Aries1A/kenagerobo/src/pyscript/Q_learning/img_forum/camera_capture_0.jpg

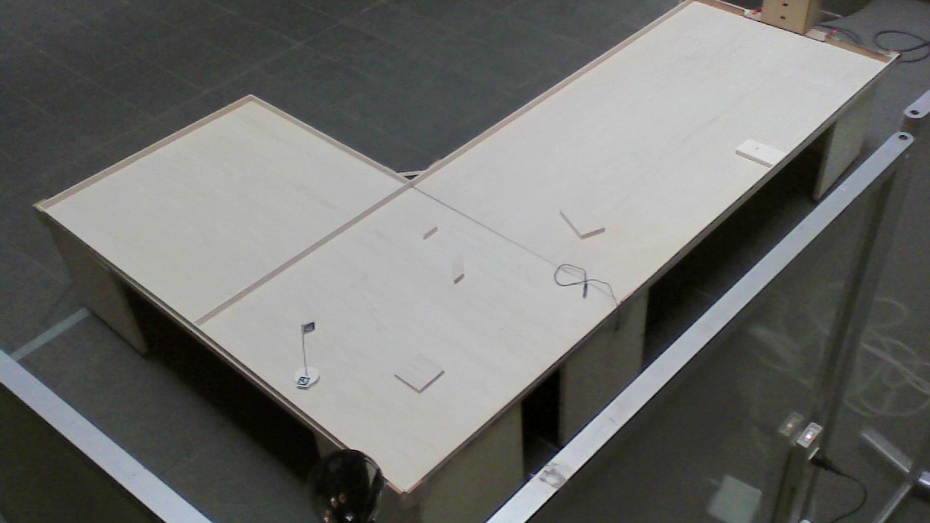
src/pyscript/Q_learning/img_forum/camera_capture_0.jpg
