Aries1A/kenagerobo/src/pyscript/Q_learning/imgs/img_forum/camera_capture_1.jpg

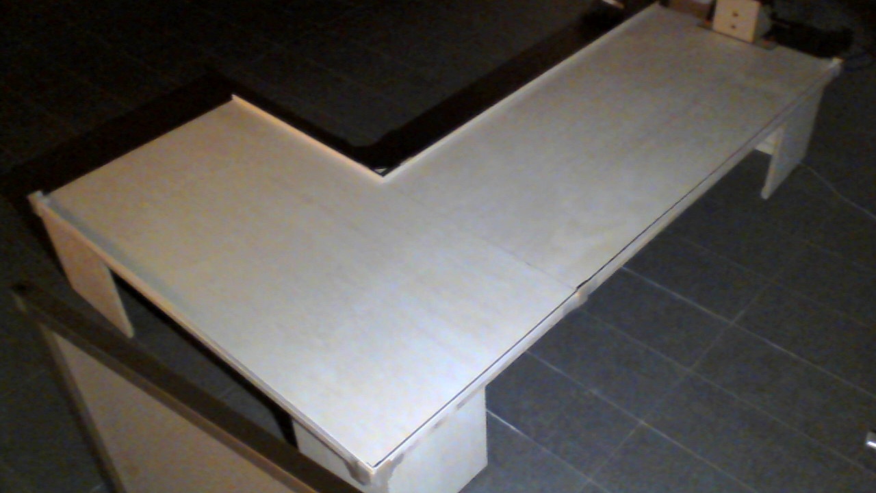
src/pyscript/Q_learning/imgs/img_forum/camera_capture_1.jpg
