Aries1A/kenagerobo/src/pyscript/Q_learning/imgs/img_forum_square/camera_capture_0.jpg

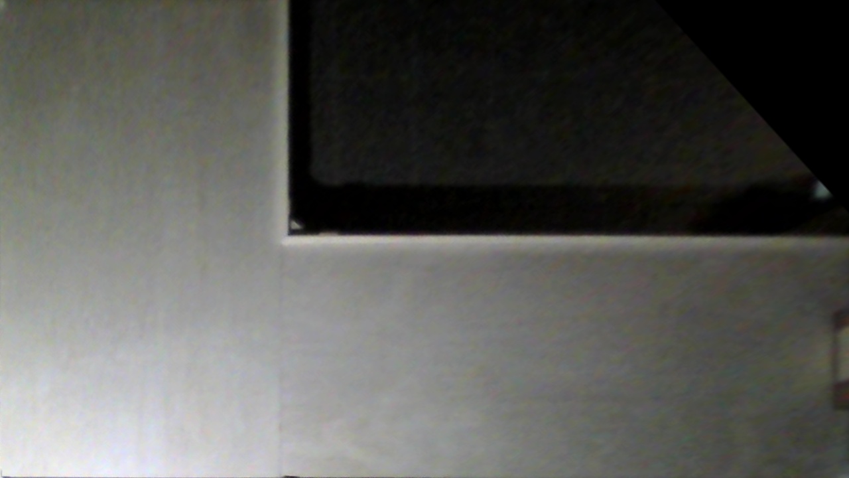
src/pyscript/Q_learning/imgs/img_forum_square/camera_capture_0.jpg
