Aries1A/kenagerobo/src/pyscript/Q_learning/imgs/img_forum_square/camera_capture_1.jpg

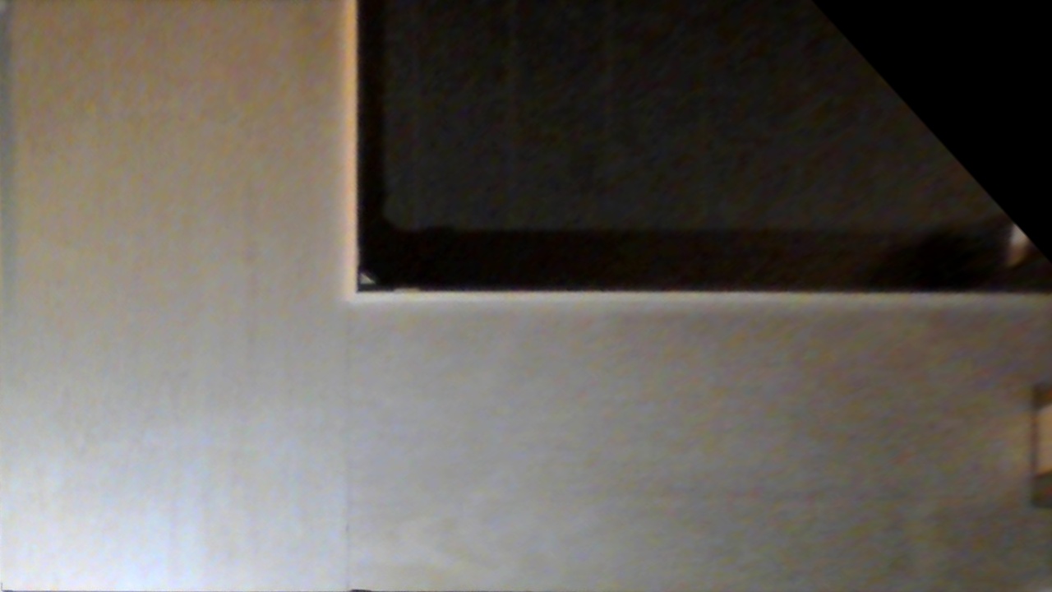
src/pyscript/Q_learning/imgs/img_forum_square/camera_capture_1.jpg
