Aries1A/kenagerobo/src/pyscript/Q_learning/imgs/img_square/147_24.jpg

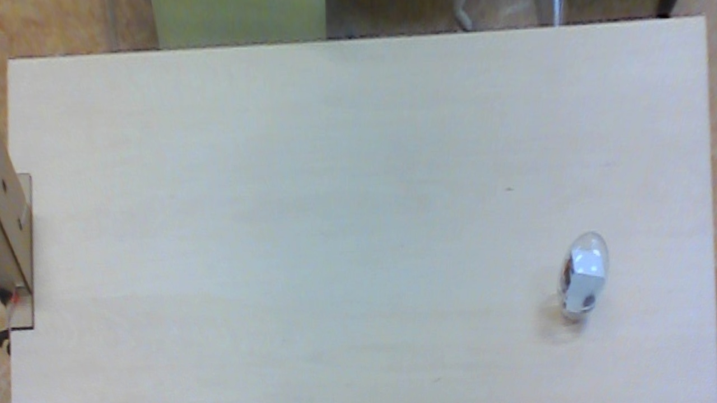
src/pyscript/Q_learning/imgs/img_square/147_24.jpg
