Aries1A/kenagerobo/src/pyscript/Q_learning/imgs/img_square/156_35_himo.jpg

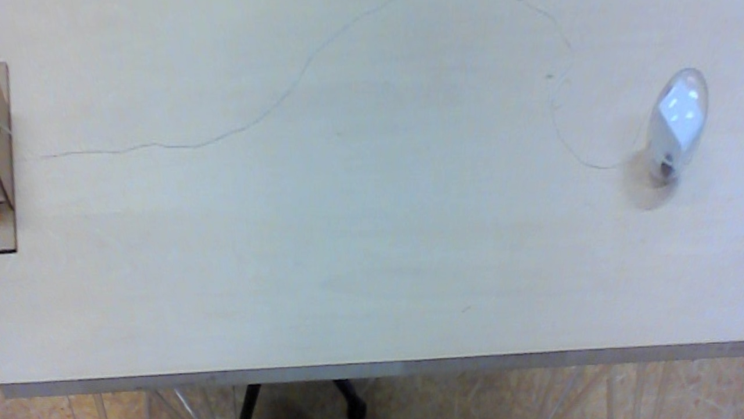
src/pyscript/Q_learning/imgs/img_square/156_35_himo.jpg
