Aries1A/kenagerobo/src/pyscript/Q_learning/imgs/img_square/180_0.jpg

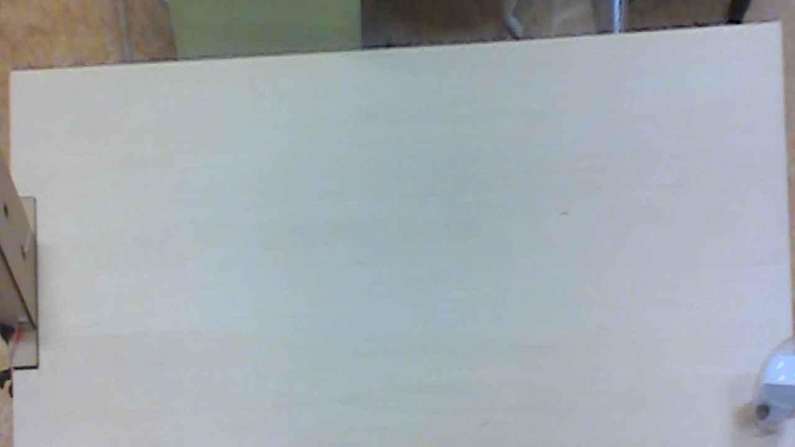
src/pyscript/Q_learning/imgs/img_square/180_0.jpg
