Aries1A/kenagerobo/src/pyscript/Q_learning/imgs/img_square/camera_capture_2.jpg

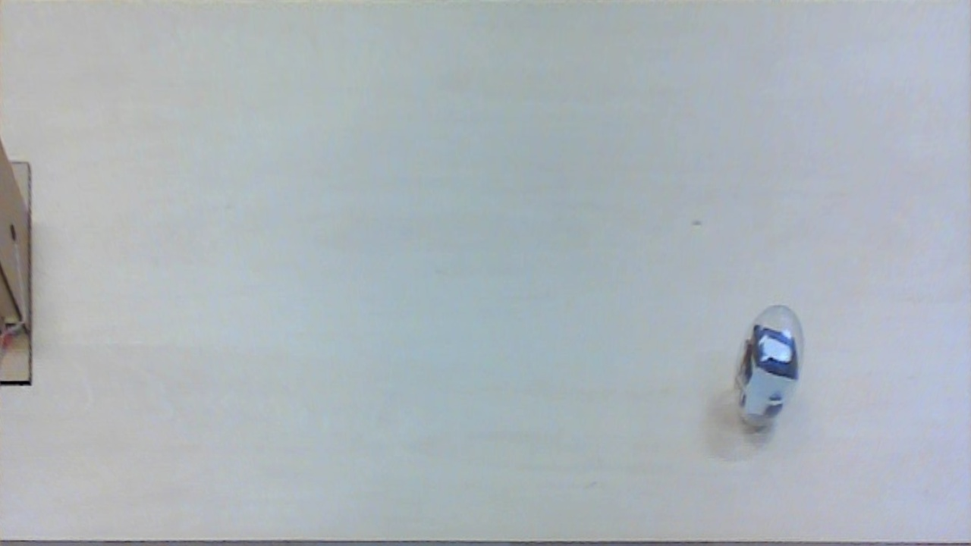
src/pyscript/Q_learning/imgs/img_square/camera_capture_2.jpg
