Aries1A/kenagerobo/src/pyscript/Q_learning/imgs/img_square/out.jpg

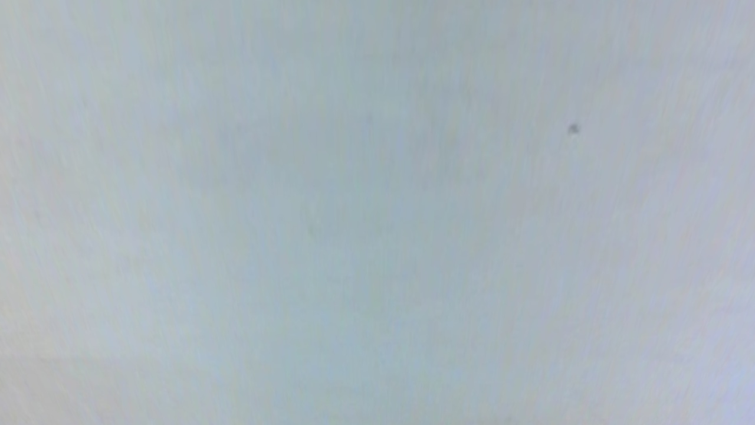
src/pyscript/Q_learning/imgs/img_square/out.jpg
