Aries1A/kenagerobo/src/pyscript/Q_learning/imgs/out.jpg

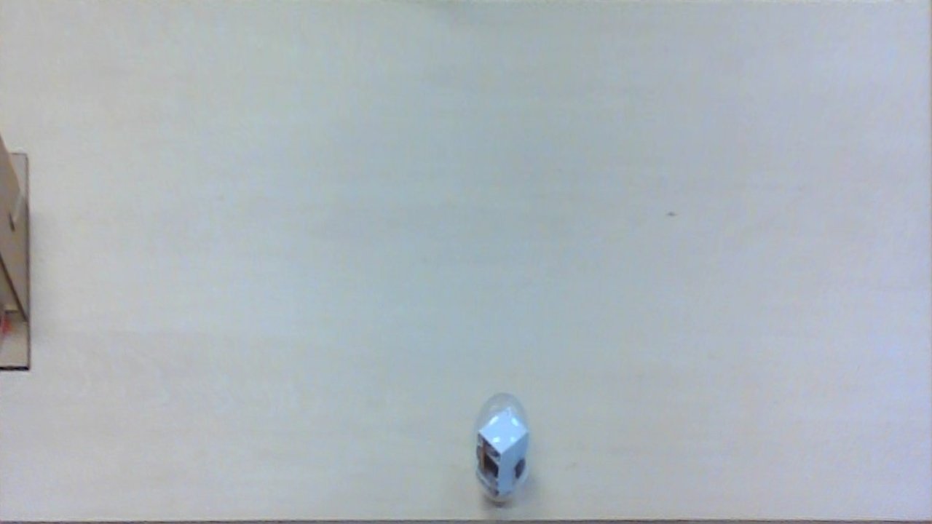
src/pyscript/Q_learning/imgs/out.jpg
